Matthewjg95/project-platypus/assets/photos/p02_thumbscrew.jpg

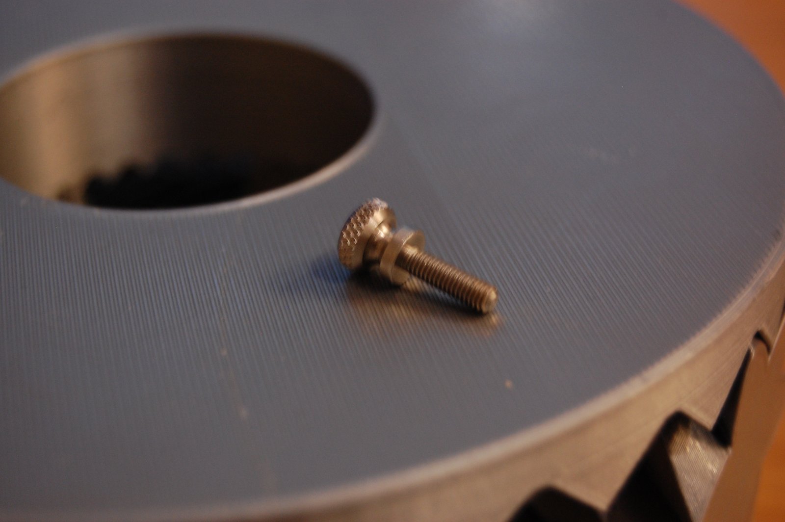
assets/photos/p02_thumbscrew.jpg
