Matthewjg95/project-platypus/assets/photos/p05_grove_cable.jpg

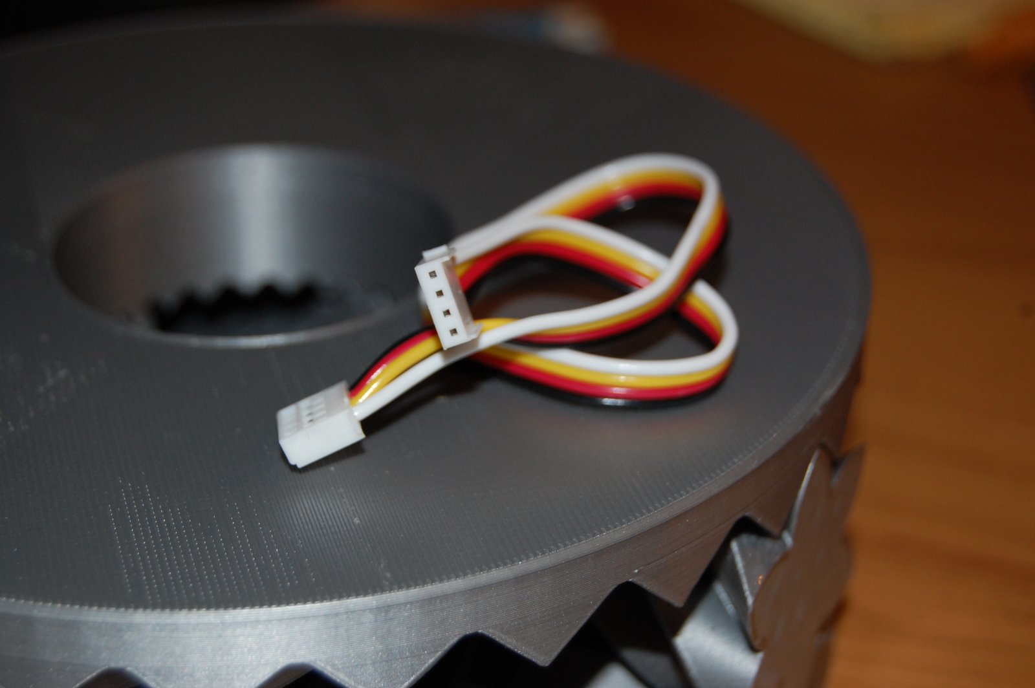
assets/photos/p05_grove_cable.jpg
