Matthewjg95/project-platypus/assets/photos/p06_tab5_pedestal.jpg

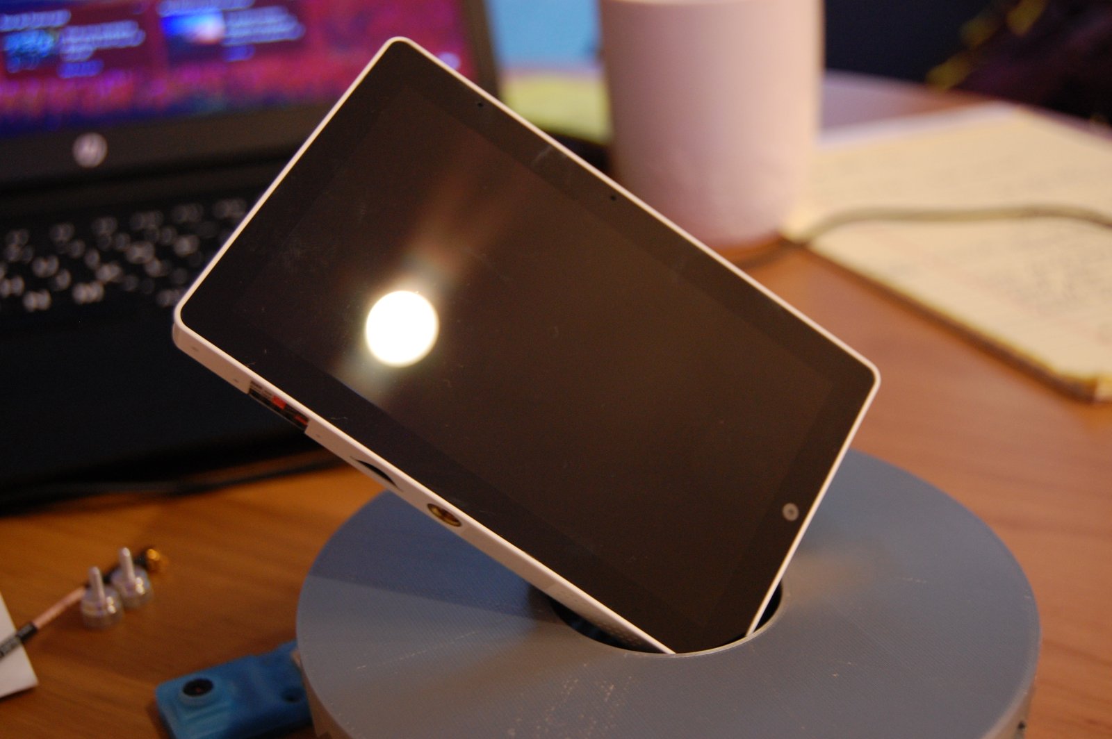
assets/photos/p06_tab5_pedestal.jpg
