Matthewjg95/project-platypus/assets/photos/p07_back_battery_campod.jpg

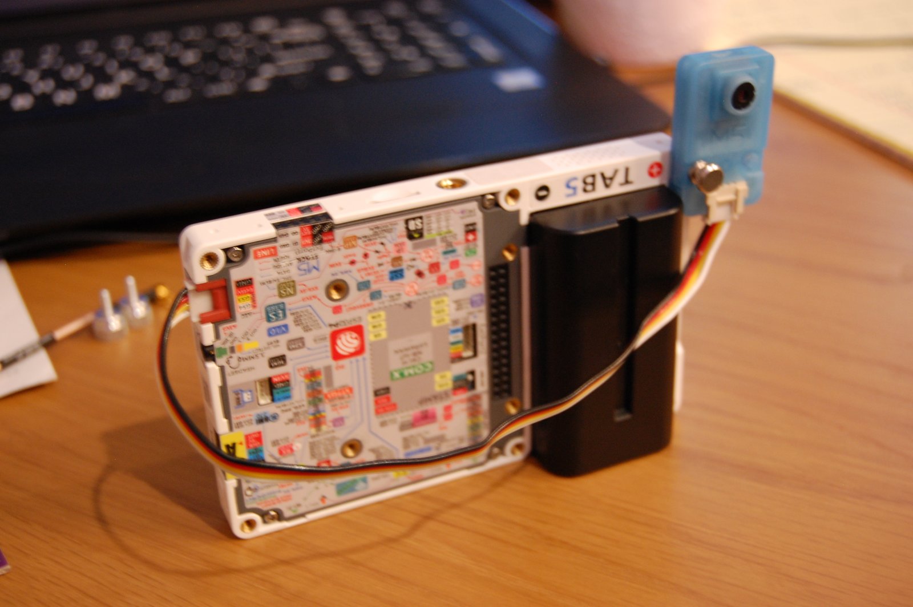
assets/photos/p07_back_battery_campod.jpg
