Matthewjg95/project-platypus/assets/photos/p08_back_panel_standoffs.jpg

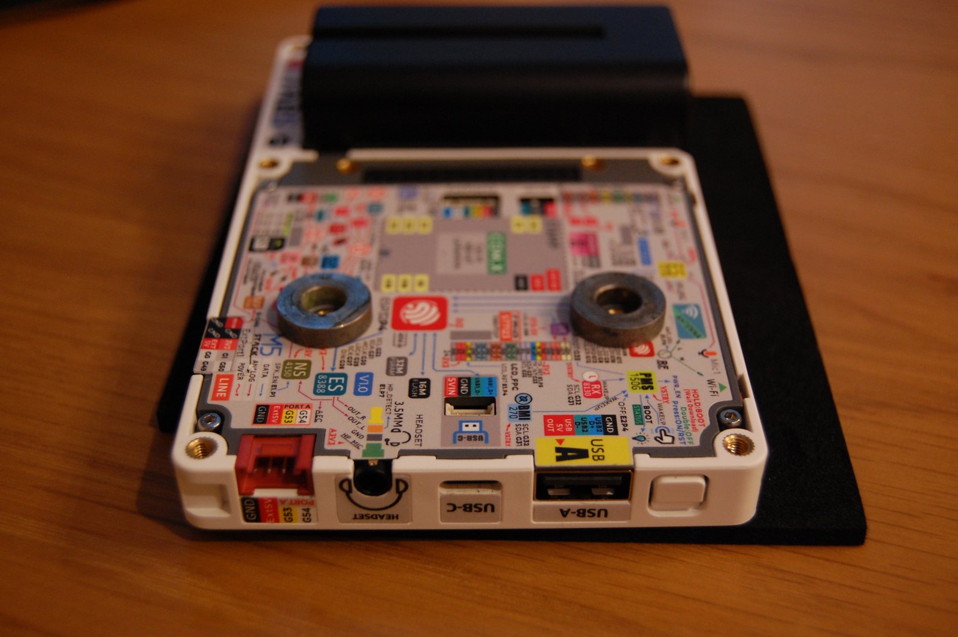
assets/photos/p08_back_panel_standoffs.jpg
