Matthewjg95/project-platypus/assets/photos/p09_hand_scale.jpg

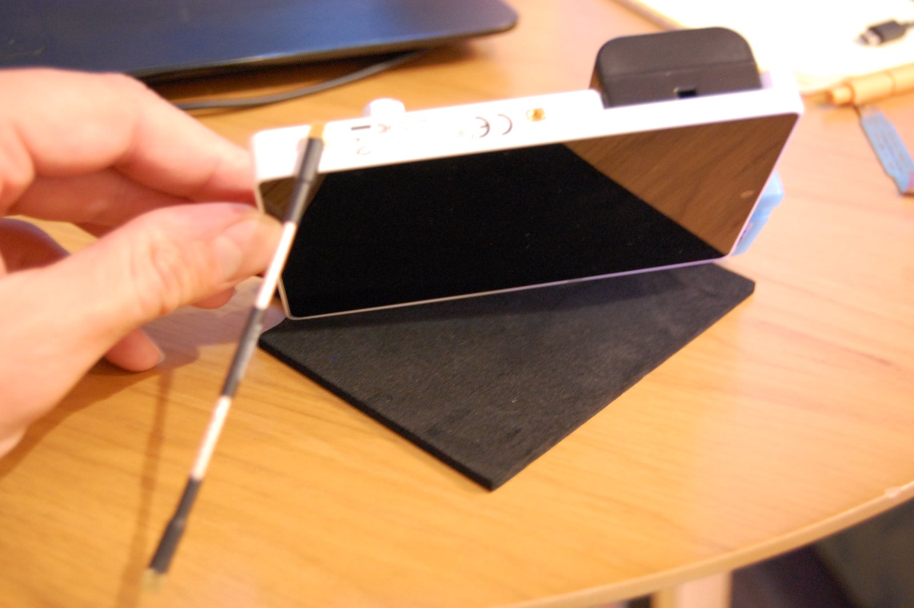
assets/photos/p09_hand_scale.jpg
