Matthewjg95/project-platypus/assets/photos/p11_camera_tether.jpg

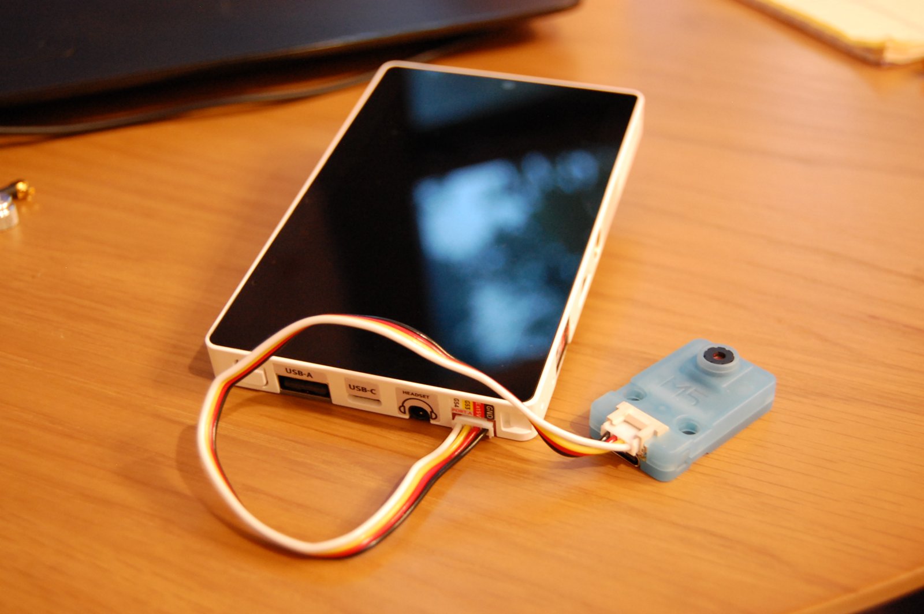
assets/photos/p11_camera_tether.jpg
