Matthewjg95/project-platypus/assets/screens/s02_home.png

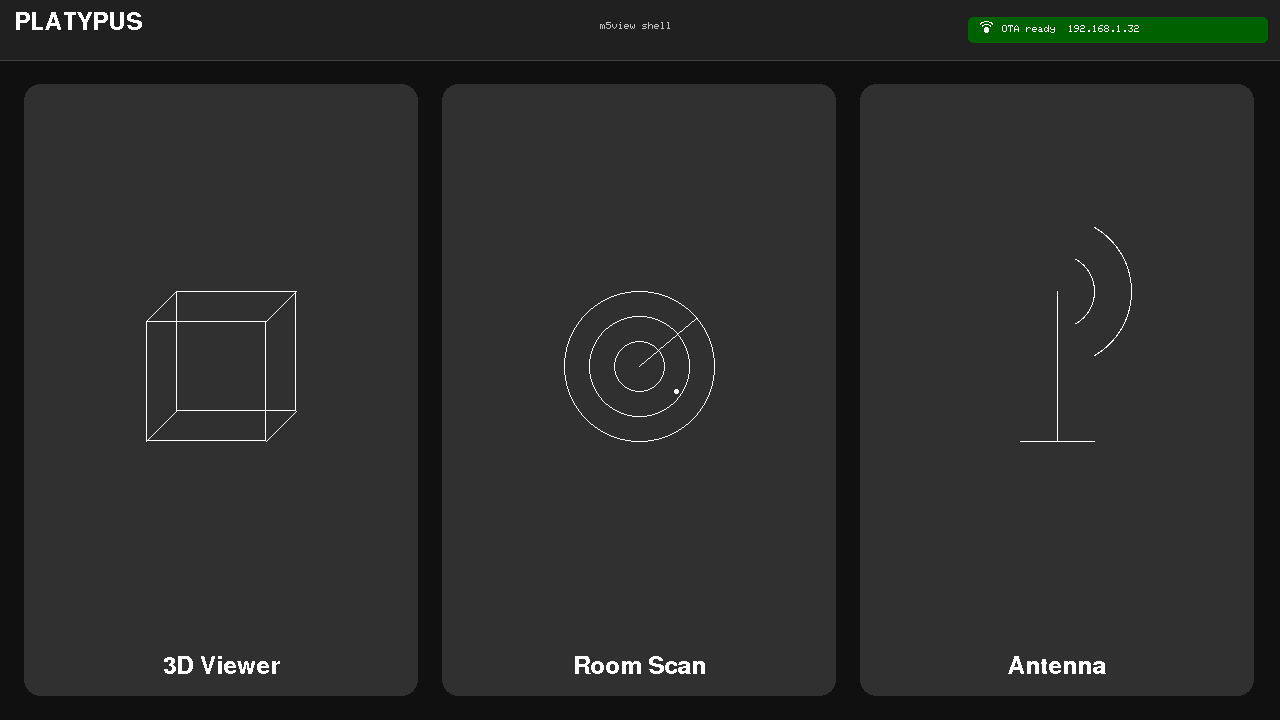
assets/screens/s02_home.png
