Matthewjg95/project-platypus/assets/screens/s03_sweep_dial.png

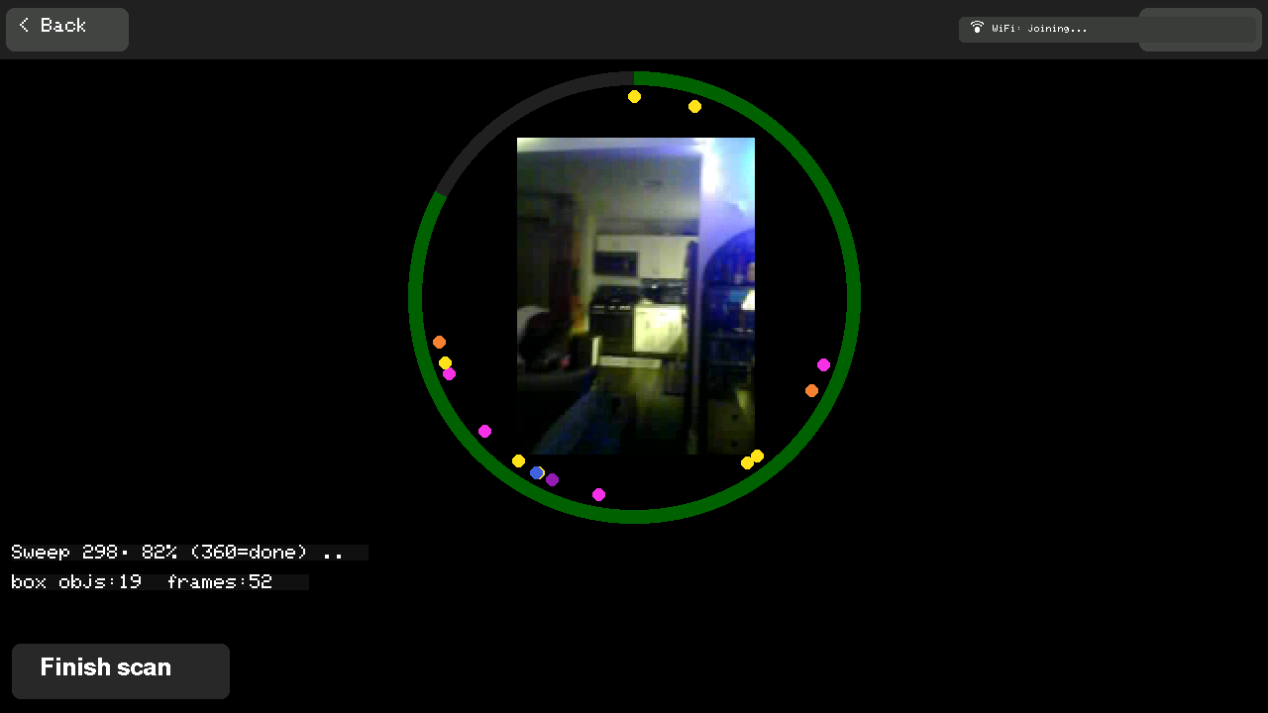
assets/screens/s03_sweep_dial.png
