Matthewjg95/project-platypus/assets/screens/s04_room_view.png

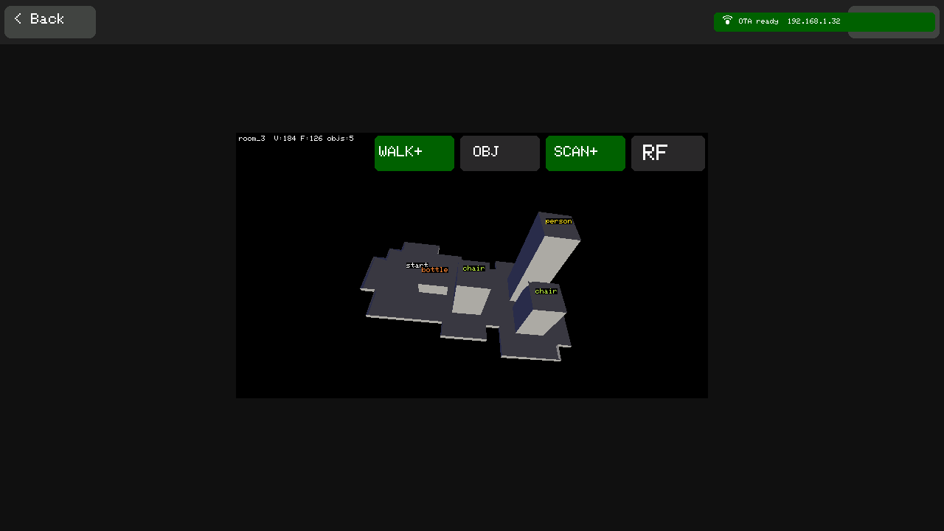
assets/screens/s04_room_view.png
