Matthewjg95/project-platypus/assets/screens/s06_rf_internal.png

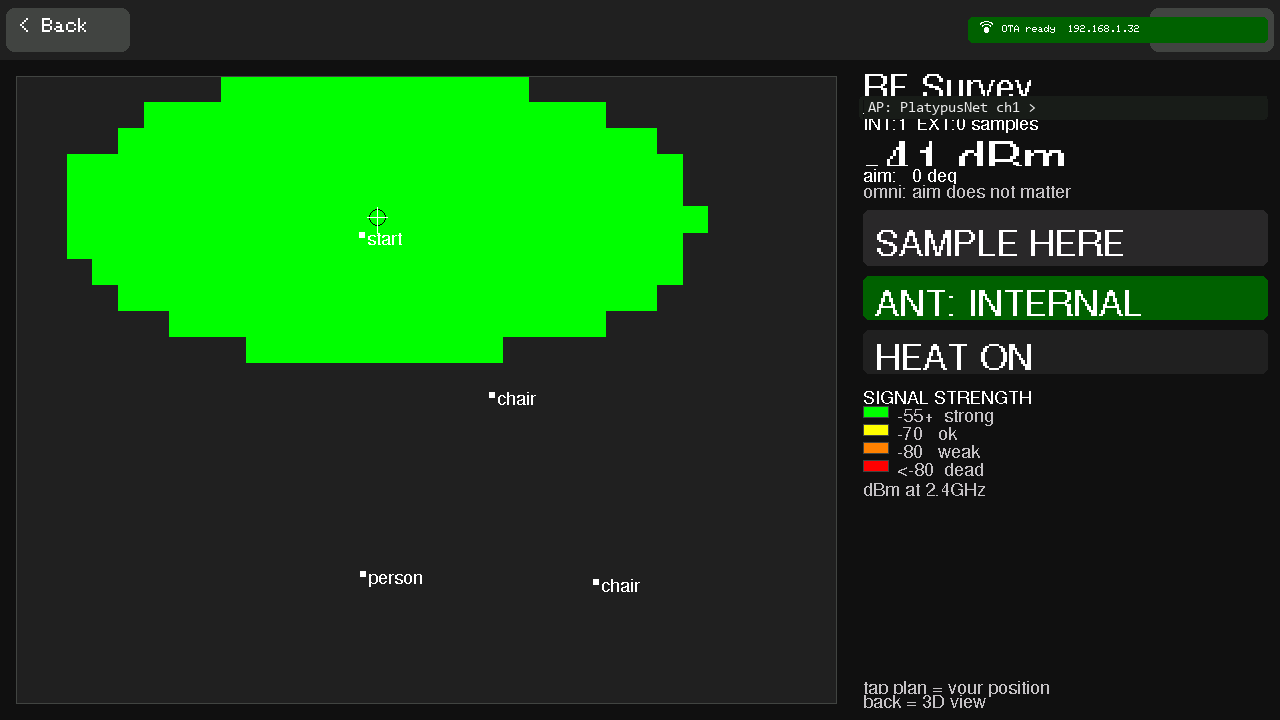
assets/screens/s06_rf_internal.png
