Matthewjg95/project-platypus/assets/screens/s07_rf_external.png

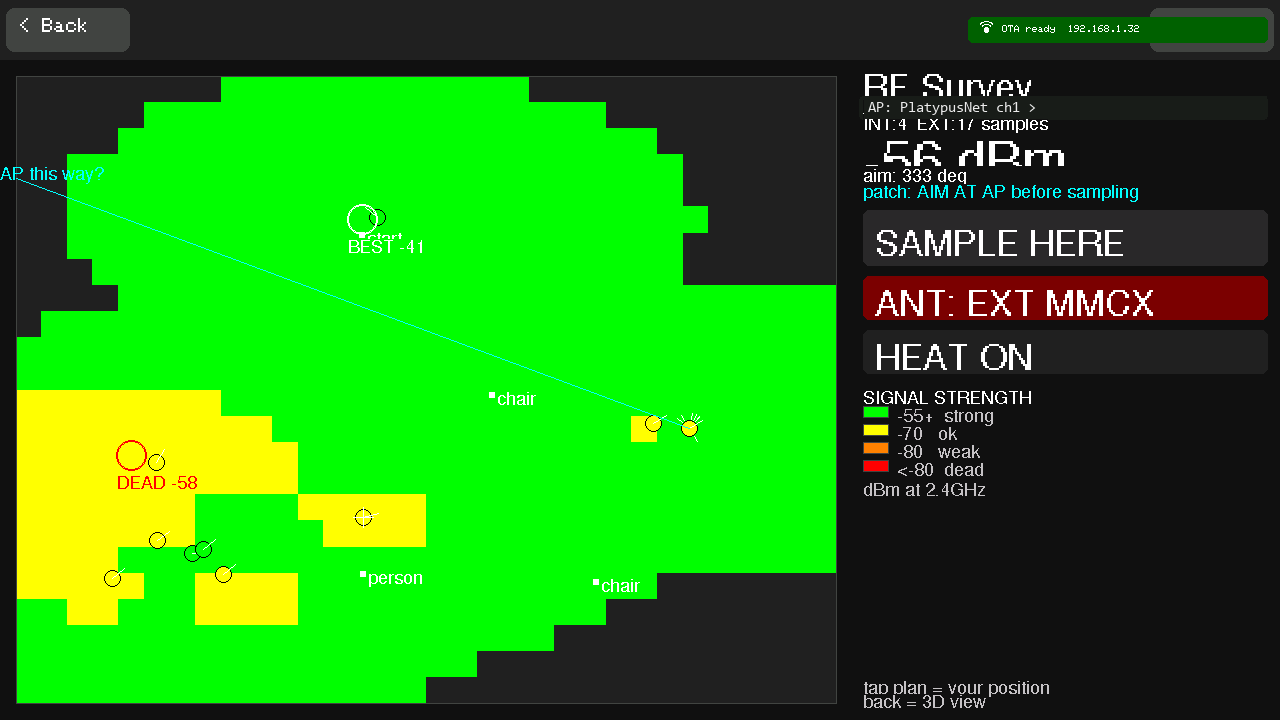
assets/screens/s07_rf_external.png
