Matthewjg95/project-platypus/assets/screens/s10_oscilloscope.png

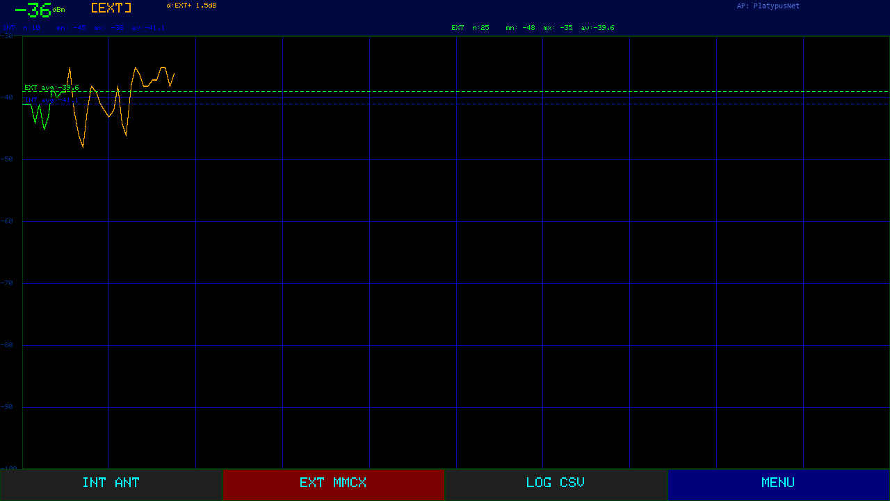
assets/screens/s10_oscilloscope.png
