Matthewjg95/project-platypus/assets/schematic_system_wiring.png

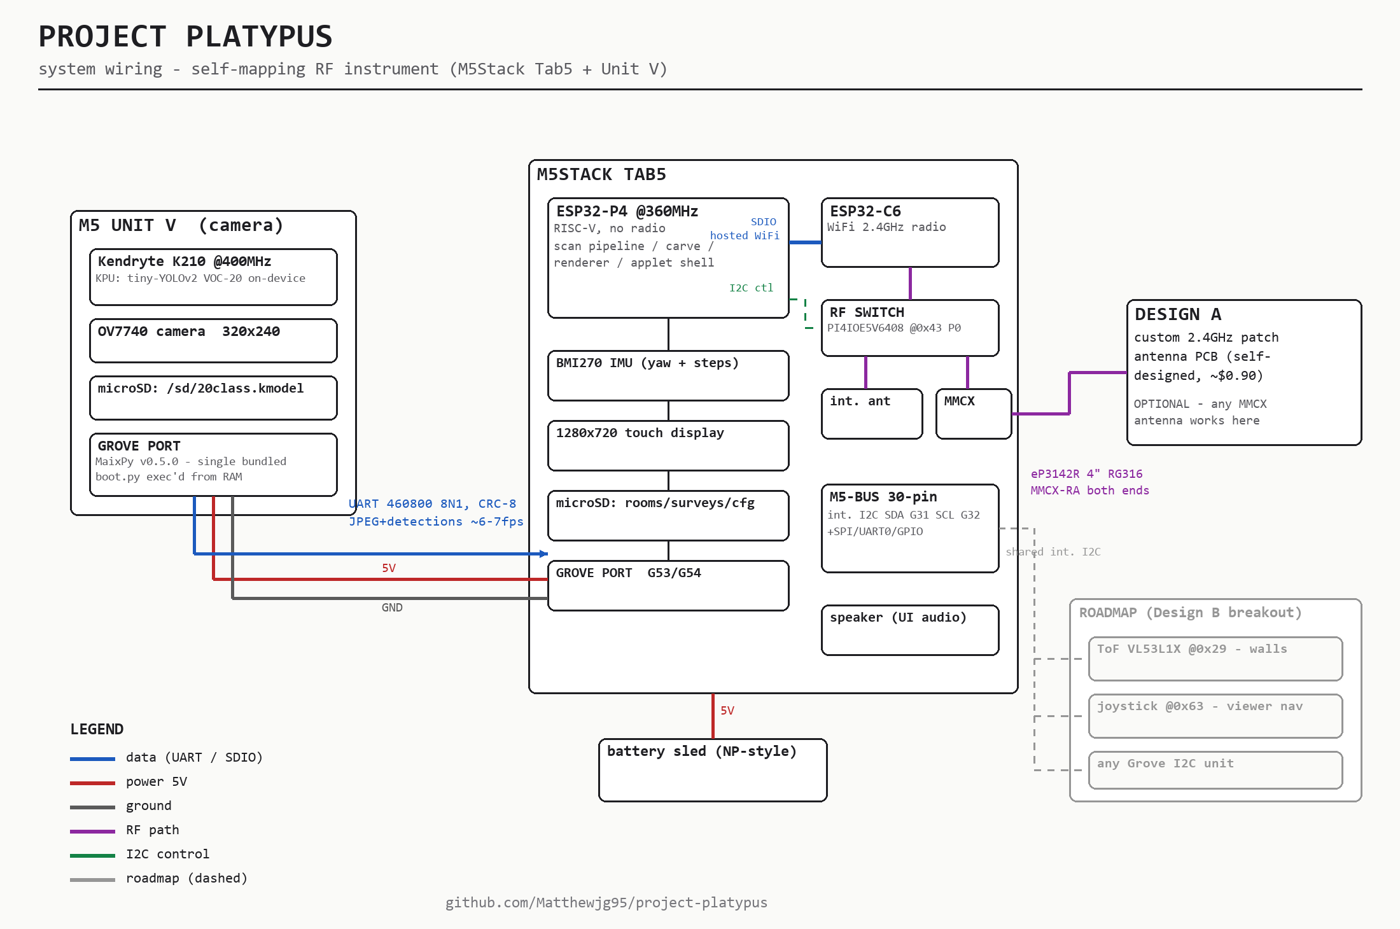
assets/schematic_system_wiring.png
