Matthewjg95/project-platypus/assets/screens/s08_building_map.png

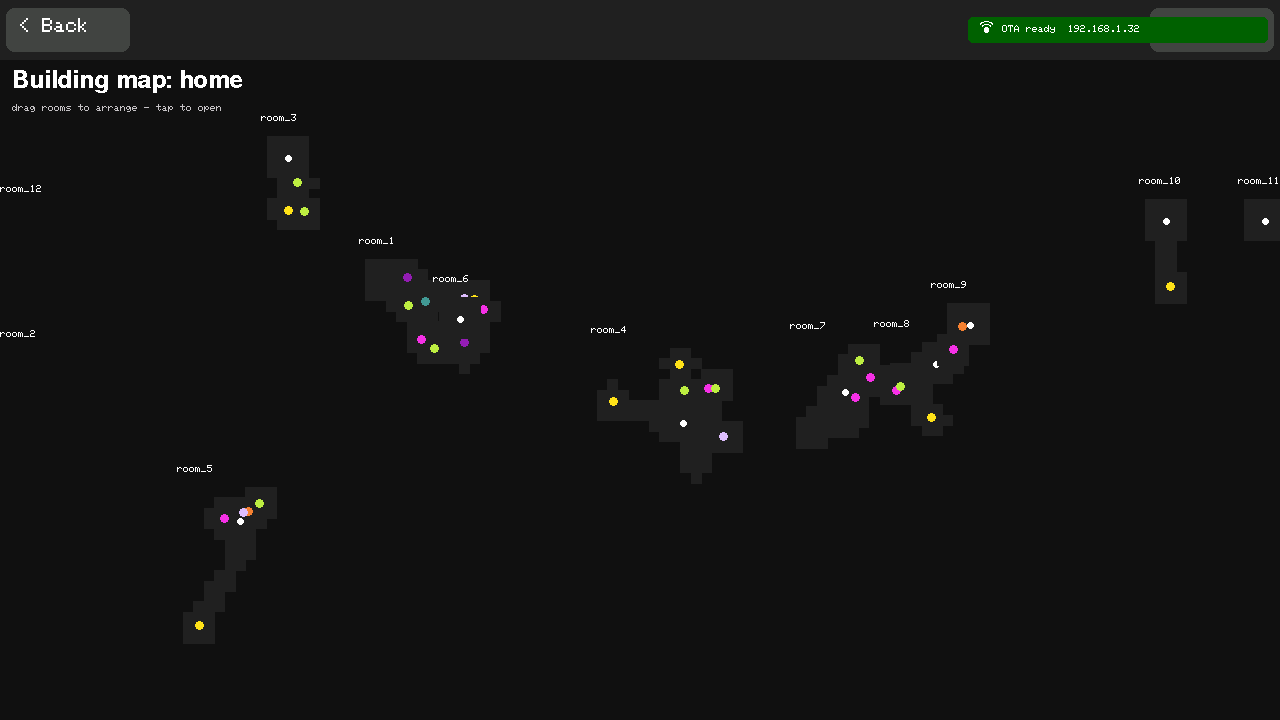
assets/screens/s08_building_map.png
