Matthewjg95/project-platypus/Tab5 3D Render/src/ui_constants.h

#pragma once

static const int BAR_H          = 60;
static const int BACK_BTN_W     = 130;
static const int SETTINGS_BTN_W = 130;
static const int TILE_COLS      = 3;
static const int TILE_ROWS      = 1;    // 3 full-height tiles: the contest story
static const int TILE_PAD       = 24;
static const int TILE_RADIUS    = 16;
static const int PANEL_H        = 500;

static const uint16_t COL_BG      = 0x1082;
static const uint16_t COL_BAR     = 0x2104;
static const uint16_t COL_BTN     = 0x4228;
static const uint16_t COL_TILE    = 0x3186;
static const uint16_t COL_PANEL   = 0x2945;
static const uint16_t COL_DIVIDER = 0x4228;
static const uint16_t COL_TEXT    = TFT_WHITE;
static const uint16_t COL_SUBTEXT = 0xC618;
static const uint16_t COL_HANDLE  = 0x7BEF;
